ElectronicCats/badge-bsides-cdmx-2024/firmware/badge/main/modules/bsides_ajolote/ajo_module.h

#pragma once
#ifndef AJO_MODULE_H
  #define AJO_MODULE_H

  #include "iot_button.h"

  #define GPIO_IN_SHITTY      2
  #define GPIO_IN_SHITTY_MASK 0b0000 << 4

  #define GPIO_SHITTY_ACTIVE_LEVEL 1
// 'AjoIDLE', 128x32px
static const unsigned char ajolote_AjoIDLE[] = {
    0x00, 0x00, 0x00, 0x00, 0x00, 0x00, 0x00, 0x00, 0x00, 0x00, 0x00, 0x00,
    0x00, 0x00, 0x00, 0x00, 0x00, 0x00, 0x00, 0x00, 0x00, 0x00, 0x00, 0x00,
    0x00, 0x00, 0x00, 0x00, 0x00, 0x00, 0x00, 0x00, 0x00, 0x00, 0x00, 0x00,
    0x00, 0x00, 0x00, 0x00, 0x00, 0x00, 0x00, 0x00, 0x00, 0x00, 0x00, 0x00,
    0x00, 0x00, 0x00, 0x00, 0x00, 0x00, 0x00, 0x00, 0x00, 0x00, 0x00, 0x00,
    0x00, 0x00, 0x00, 0x00, 0x00, 0x00, 0x00, 0x00, 0x00, 0x00, 0x00, 0x00,
    0x00, 0x00, 0x00, 0x00, 0x07, 0xc0, 0x00, 0x00, 0x00, 0x00, 0x00, 0x3e,
    0x00, 0x00, 0x00, 0x00, 0x00, 0x00, 0x00, 0x00, 0x3f, 0xc0, 0x00, 0x00,
    0x00, 0x00, 0x00, 0x7f, 0xe0, 0x00, 0x00, 0x00, 0x00, 0x00, 0x00, 0x01,
    0xf9, 0xc0, 0x00, 0x00, 0x00, 0x00, 0x00, 0x71, 0x78, 0x00, 0x00, 0x00,
    0x00, 0x00, 0x00, 0x03, 0x83, 0xc0, 0x0f, 0x80, 0x00, 0x3f, 0x80, 0x30,
    0x5c, 0x00, 0x00, 0x00, 0x00, 0x00, 0x00, 0x07, 0x03, 0x80, 0x7f, 0x80,
    0x00, 0x39, 0xf0, 0x38, 0x1e, 0x00, 0x00, 0x07, 0xff, 0x00, 0x00, 0x1f,
    0x07, 0x83, 0xe3, 0x80, 0x00, 0x1c, 0x3e, 0x1e, 0x2f, 0xe0, 0x03, 0xff,
    0xff, 0xfe, 0x0f, 0xf8, 0x1f, 0x0f, 0x87, 0x00, 0x00, 0x0e, 0x07, 0x07,
    0x80, 0xff, 0x7f, 0xff, 0x7f, 0xff, 0xfe, 0x00, 0x78, 0x1c, 0x0e, 0x00,
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
static const unsigned char* ajolote_allArray[4] = {
    ajolote_AjoIDLE, ajolote_AjoLeft, ajolote_AjoIDLE, ajolote_AjoRight};

bool ajo_module_display_animation();
void ajo_module_init(void);
bool ajo_module_get_state();
void ajo_module_delete_task();

#endif  // AJO_MODULE_H
